ARTS-Laboratory/Drone-Delivered-Vibration-Sensor/system_design/Forth/V0.2.0/Hardware/CAD/Images - In Progress Designs/Permanent Magnet Cap.png

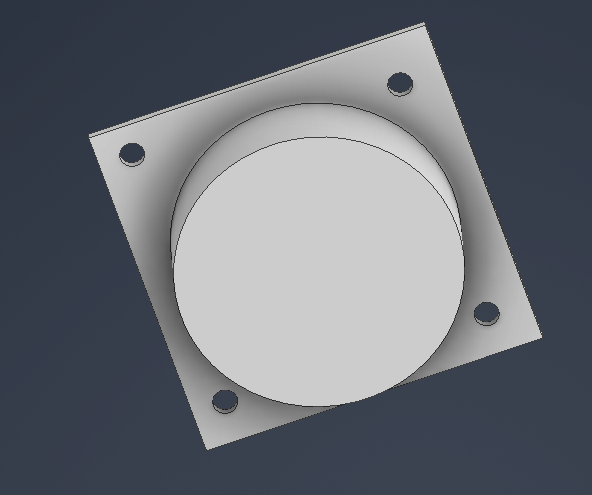
system_design/Forth/V0.2.0/Hardware/CAD/Images - In Progress Designs/Permanent Magnet Cap.png
