ARTS-Laboratory/Drone-Delivered-Vibration-Sensor/system_design/Forth/V0.2.0/Hardware/CAD/Images - In Progress Designs/Standoffs for PCB screws (which of the two options).png

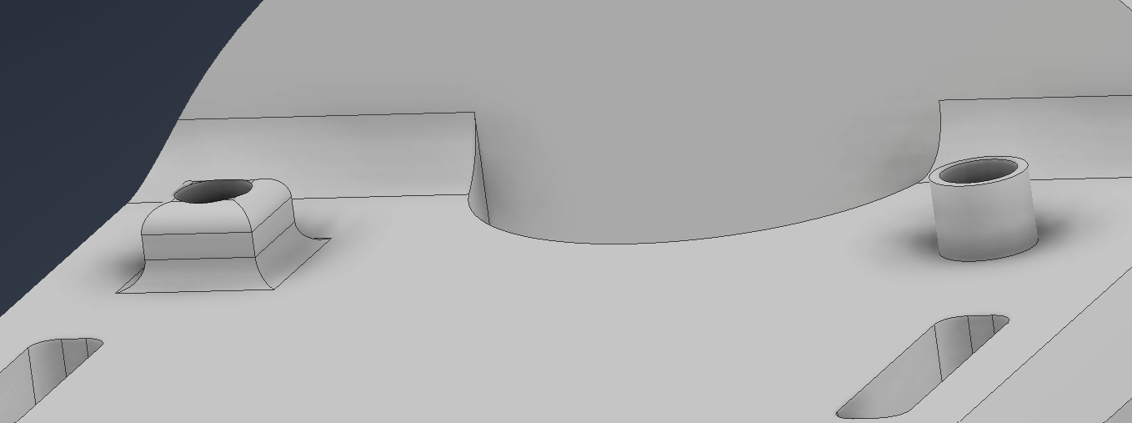
system_design/Forth/V0.2.0/Hardware/CAD/Images - In Progress Designs/Standoffs for PCB screws (which of the two options).png
