ARTS-Laboratory/Drone-Delivered-Vibration-Sensor/system_design/International Gateway/V0.1/Software/Arduino/Shaker Data Collection/001_FFT_Smoothed_Spectrum_Comparison.png

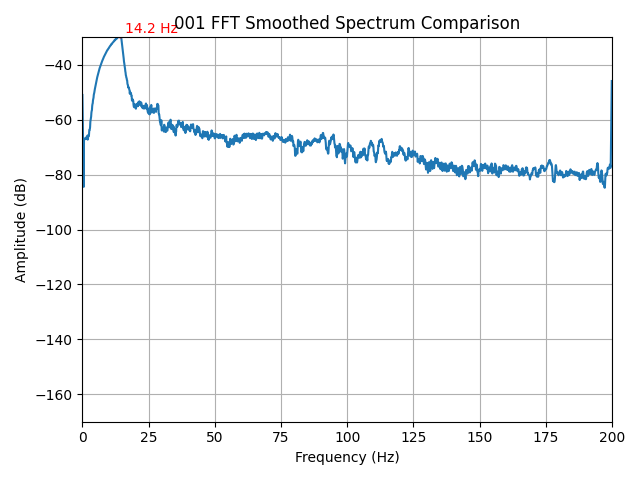
system_design/International Gateway/V0.1/Software/Arduino/Shaker Data Collection/001_FFT_Smoothed_Spectrum_Comparison.png
