ARTS-Laboratory/Drone-Delivered-Vibration-Sensor/system_design/International Gateway/V0.1/Software/Arduino/Shaker Data Collection/005 Training Error vs Epoch.png

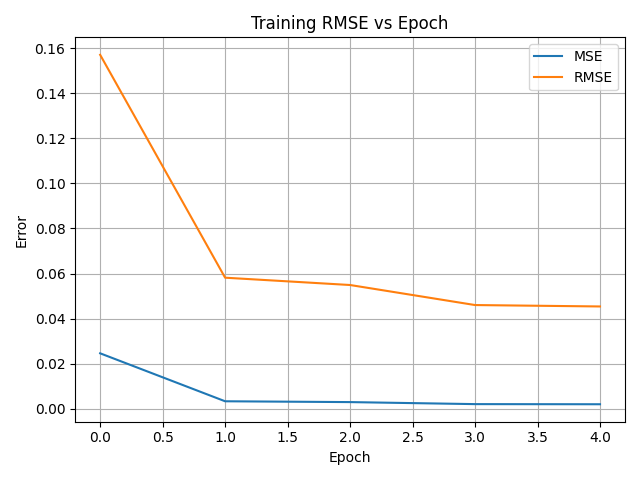
system_design/International Gateway/V0.1/Software/Arduino/Shaker Data Collection/005 Training Error vs Epoch.png
