ARTS-Laboratory/Drone-Delivered-Vibration-Sensor/system_design/International Gateway/V0.1/Software/Arduino/Shaker Data Collection/014_10Epoch_Training_Error_vs_Epoch.png

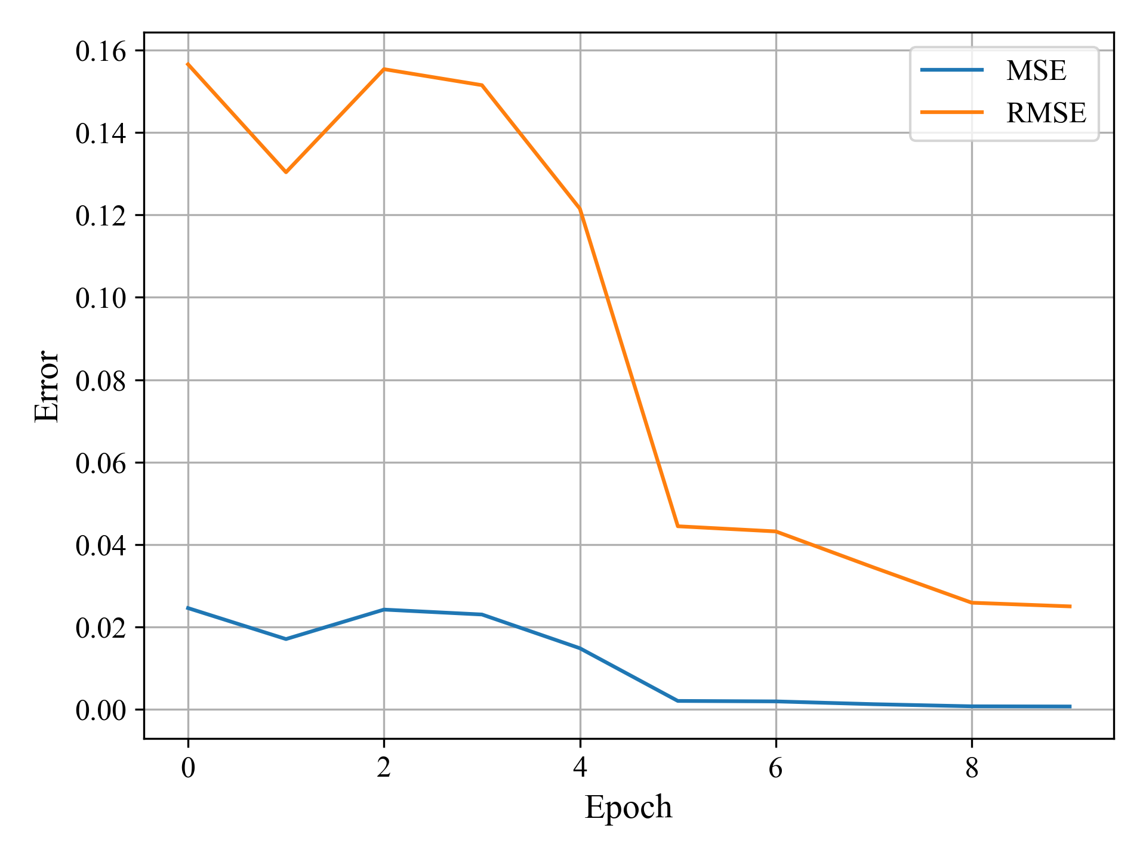
system_design/International Gateway/V0.1/Software/Arduino/Shaker Data Collection/014_10Epoch_Training_Error_vs_Epoch.png
