ARTS-Laboratory/Drone-Delivered-Vibration-Sensor/system_design/International Gateway/V0.1/Software/Arduino/Shaker Data Collection/DATA001_FRF_Magnitude.png

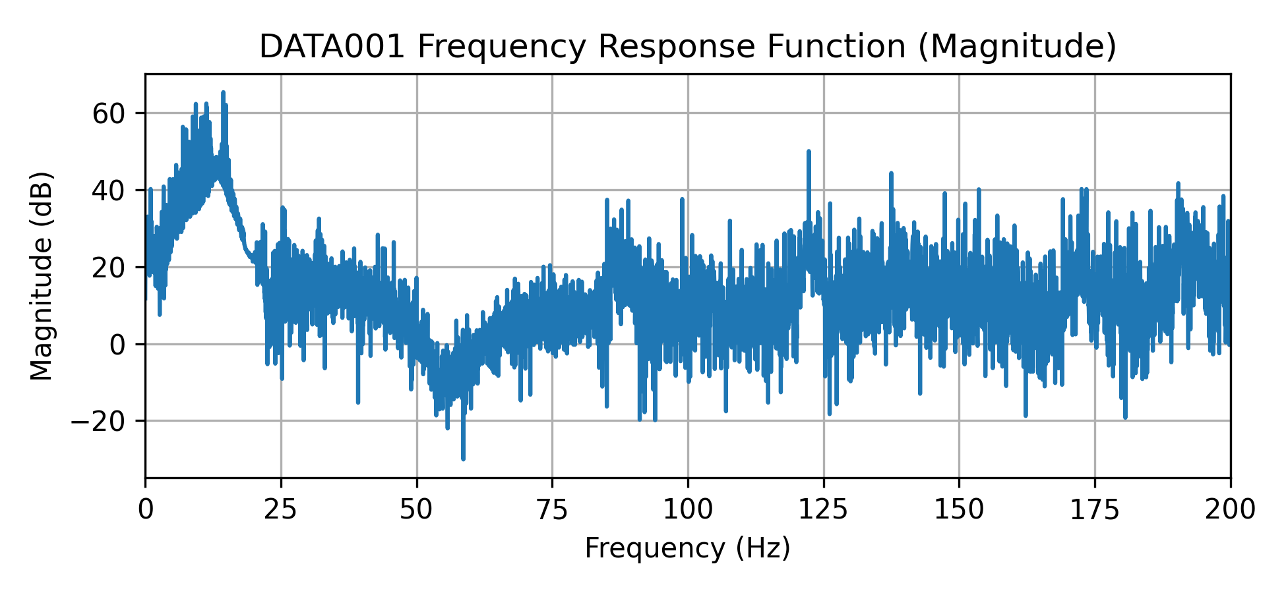
system_design/International Gateway/V0.1/Software/Arduino/Shaker Data Collection/DATA001_FRF_Magnitude.png
