ARTS-Laboratory/Drone-Delivered-Vibration-Sensor/system_design/International Gateway/V0.1/Software/Arduino/Shaker Data Collection/dataset_collection/dataset-collection/improved-dataset-collection/ZoomedInImpulse.png

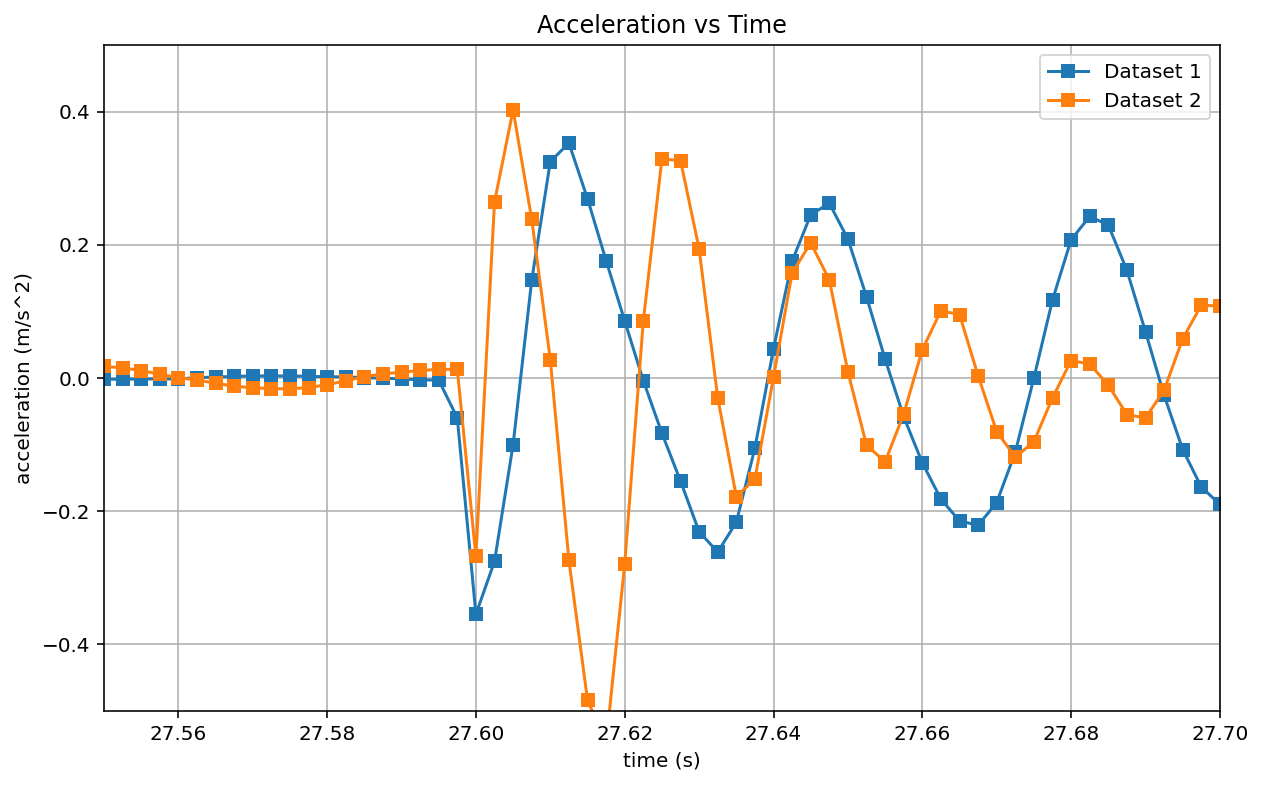
system_design/International Gateway/V0.1/Software/Arduino/Shaker Data Collection/dataset_collection/dataset-collection/improved-dataset-collection/ZoomedInImpulse.png
