ARTS-Laboratory/Drone-Delivered-Vibration-Sensor/system_design/International Gateway/V0.1/Software/Arduino/Shaker Data Collection/Runs/Run_001_Epoch20_Batch16_Window400/014_20Epoch_Zoom_Acceleration_Comparison.png

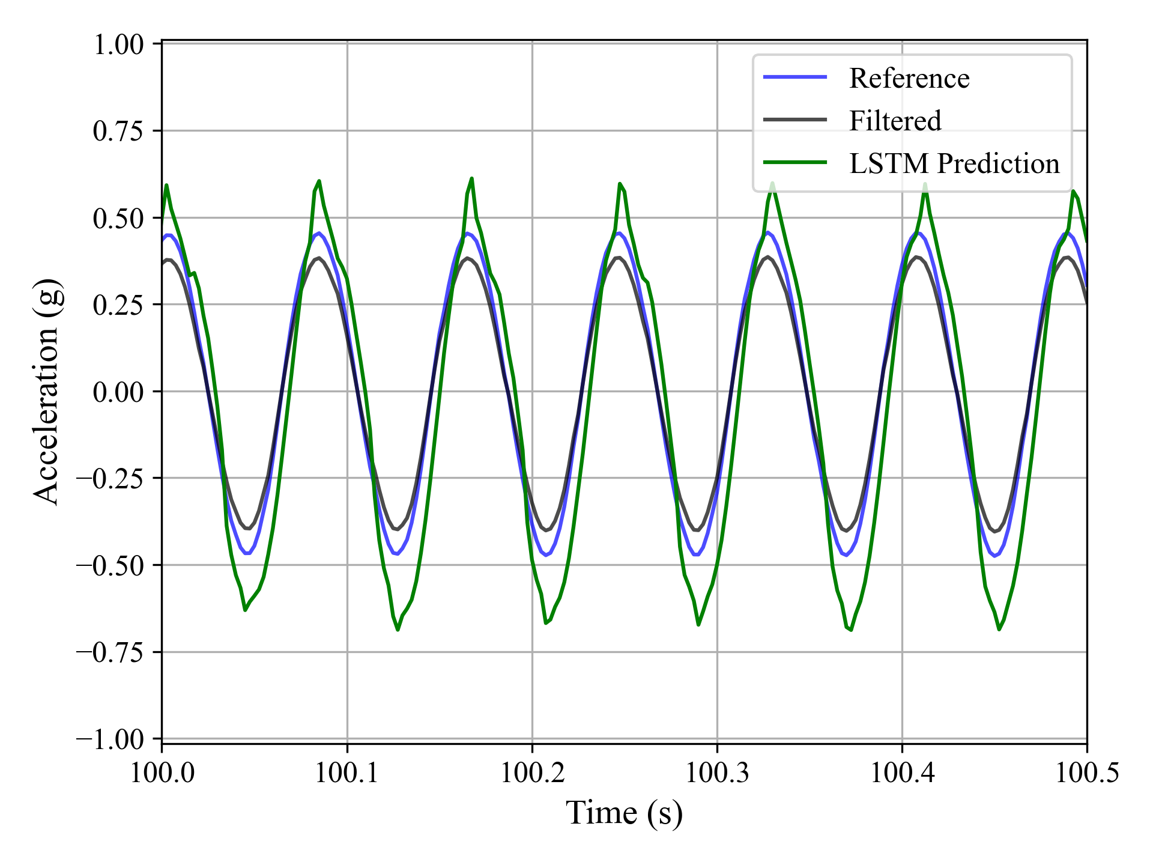
system_design/International Gateway/V0.1/Software/Arduino/Shaker Data Collection/Runs/Run_001_Epoch20_Batch16_Window400/014_20Epoch_Zoom_Acceleration_Comparison.png
