ARTS-Laboratory/Drone-Delivered-Vibration-Sensor/system_design/International Gateway/V0.1/Software/test/reduced.csv

-5.280582979321479797e-02
-6.273836642503738403e-02
-6.120144948363304138e-02
-5.868064984679222107e-02
-5.747686699032783508e-02
-5.670031160116195679e-02
-5.480265989899635315e-02
-5.214745178818702698e-02
-4.811622947454452515e-02
-4.461257904767990112e-02
-3.961358591914176941e-02
-3.492707386612892151e-02
-3.026051446795463562e-02
-2.505939267575740814e-02
-1.904052495956420898e-02
-1.265662536025047302e-02
-5.546108819544315338e-03
7.930994033813476562e-04
7.546235807240009308e-03
1.386597938835620880e-02
2.126452513039112091e-02
2.834310196340084076e-02
3.354794532060623169e-02
3.958639502525329590e-02
4.564755037426948547e-02
5.100083723664283752e-02
5.439259484410285950e-02
5.936903133988380432e-02
6.369995325803756714e-02
6.544636189937591553e-02
6.805902719497680664e-02
6.887361407279968262e-02
6.899196654558181763e-02
6.766168773174285889e-02
6.606276333332061768e-02
6.420896947383880615e-02
6.054136157035827637e-02
5.761456862092018127e-02
5.377897247672080994e-02
4.863581433892250061e-02
4.405733942985534668e-02
3.838369250297546387e-02
3.206370398402214050e-02
2.472146973013877869e-02
1.924117468297481537e-02
1.180394738912582397e-02
3.609195118770003319e-03
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
