ARTS-Laboratory/Drone-Delivered-Vibration-Sensor/system_design/International Gateway/V0.1/Software/test/uncompressed.csv

-2.346628531813621521e-02
-4.012515023350715637e-02
-5.351005122065544128e-02
-6.720842421054840088e-02
-8.011138439178466797e-02
-9.090606123208999634e-02
-9.889101982116699219e-02
-1.043778061866760254e-01
-1.086088269948959351e-01
-1.113042235374450684e-01
-1.120164915919303894e-01
-1.100497022271156311e-01
-1.058954596519470215e-01
-1.001832112669944763e-01
-9.353651106357574463e-02
-8.547334372997283936e-02
-7.548370212316513062e-02
-6.431892514228820801e-02
-5.195856466889381409e-02
-3.988573327660560608e-02
-2.724938839673995972e-02
-1.224021427333354950e-02
3.133099293336272240e-03
1.735226809978485107e-02
3.115513175725936890e-02
4.627240449190139771e-02
6.159320101141929626e-02
7.443114370107650757e-02
8.581387996673583984e-02
9.724640101194381714e-02
1.062897816300392151e-01
1.132814735174179077e-01
1.183985844254493713e-01
1.211772039532661438e-01
1.205646246671676636e-01
1.172411367297172546e-01
1.122154220938682556e-01
1.044882982969284058e-01
9.472470730543136597e-02
8.389565348625183105e-02
7.190800458192825317e-02
5.852592736482620239e-02
4.327798634767532349e-02
2.688993141055107117e-02
9.296176955103874207e-03
-7.254051975905895233e-03
-2.285750024020671844e-02
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
