ARTS-Laboratory/Drone-Delivered-Vibration-Sensor/media/test plot edit2.png

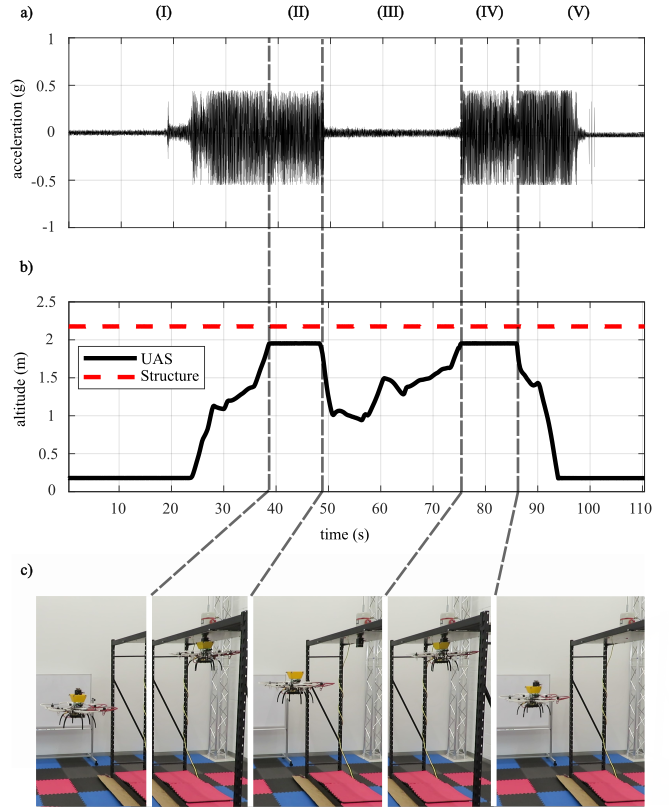
media/test plot edit2.png
