ARTS-Laboratory/Drone-Delivered-Vibration-Sensor/system_design/Brooklyn/V0.5/Hardware/Circuit/main_board/Vibration_Sensor/Vibration_Sensor.kicad_sch

## KiCad design system_design/Brooklyn/V0.5/Hardware/Circuit/main_board/Vibration_Sensor/Vibration_Sensor.kicad_sch (2023-06-23)

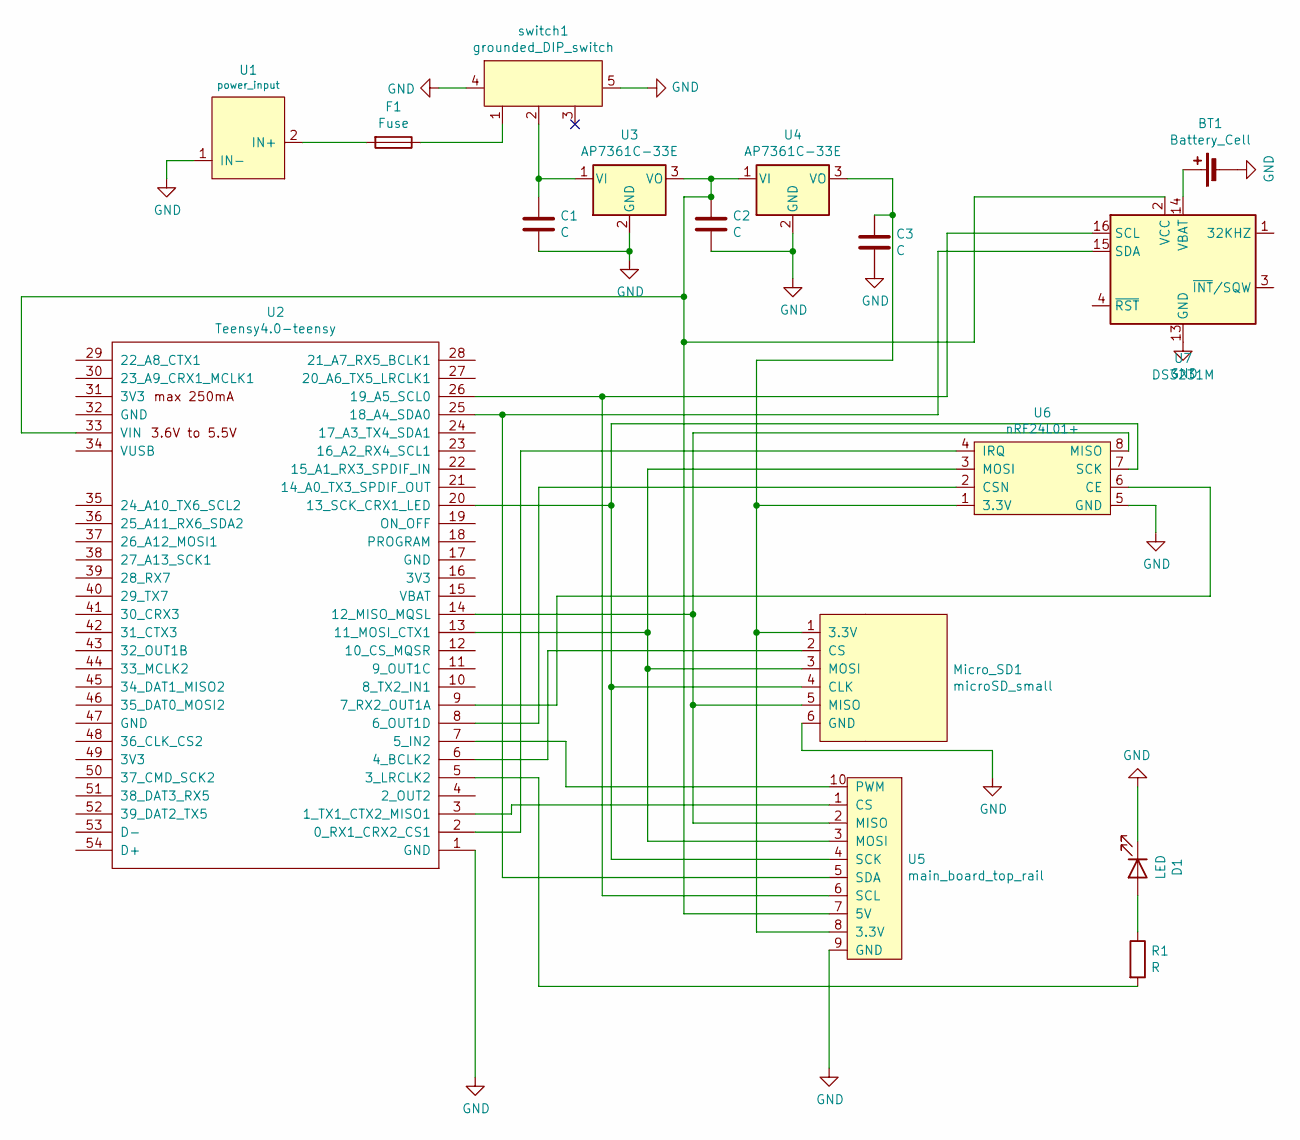
[picture p122: schematic Vibration_Sensor.kicad_sch]

Parts:
BT1: Battery_Cell; battery_holder_10mm
C1, C2, C3: C; C_1206_3216Metric_Pad1.33x1.80mm_HandSolder
D1: LED; LED_D3.0mm
F1: Fuse; C_1206_3216Metric_Pad1.33x1.80mm_HandSolder
Micro_SD1: microSD_small; small_microSD_v2
R1: R; R_1206_3216Metric_Pad1.30x1.75mm_HandSolder
U1: power_input; XT60PW
U2: Teensy4.0-teensy; teensy4.0
U3, U4: AP7361C-33E; SOT-223-3_TabPin2
U5: main_board_top_rail; top_rail
U6: nRF24L01+
U7: DS3231M; SOIC-16W_7.5x10.3mm_P1.27mm
switch1: grounded_DIP_switch; grounded_switch

Connections:
GND: BT1.2 (-), C1.2, C2.2, C3.2, D1.1 (K), Micro_SD1.6 (GND), U1.1 (IN-), U2.1 (GND), U3.2 (GND), U4.2 (GND), U5.9 (GND), U6.5 (GND), U7.5 (GND), U7.6 (GND), U7.7 (GND), U7.8 (GND), U7.9 (GND), U7.10 (GND), U7.11 (GND), U7.12 (GND), U7.13 (GND), switch1.4, switch1.5
unnamed: BT1.1 (+), U7.14 (VBAT)
unnamed: C1.1, U3.1 (VI), switch1.2
unnamed: C2.1, U2.33 (VIN), U3.3 (VO), U4.1 (VI), U5.7 (5V), U7.2 (VCC)
unnamed: C3.1, Micro_SD1.1 (3.3V), U4.3 (VO), U5.8 (3.3V), U6.1 (3.3V)
unnamed: D1.2 (A), R1.1
unnamed: F1.1, switch1.1
unnamed: F1.2, U1.2 (IN+)
unnamed: Micro_SD1.2 (CS), U2.6 (4_BCLK2)
unnamed: Micro_SD1.3 (MOSI), U2.13 (11_MOSI_CTX1), U5.3 (MOSI), U6.3 (MOSI)
unnamed: Micro_SD1.4 (CLK), U2.20 (13_SCK_CRX1_LED), U5.4 (SCK), U6.7 (SCK)
unnamed: Micro_SD1.5 (MISO), U2.14 (12_MISO_MQSL), U5.2 (MISO), U6.8 (MISO)
unnamed: R1.2, U2.5 (3_LRCLK2)
unnamed: U2.2 (0_RX1_CRX2_CS1), U6.4 (IRQ)
unnamed: U2.3 (1_TX1_CTX2_MISO1), U5.1 (CS)
unnamed: U2.7 (5_IN2), U5.10 (PWM)
unnamed: U2.8 (6_OUT1D), U6.2 (CSN)
unnamed: U2.9 (7_RX2_OUT1A), U6.6 (CE)
unnamed: U2.25 (18_A4_SDA0), U5.5 (SDA), U7.15 (SDA)
unnamed: U2.26 (19_A5_SCL0), U5.6 (SCL), U7.16 (SCL)
