ARTS-Laboratory/Drone-Delivered-Vibration-Sensor/system_design/Brooklyn/V0.5/Software/Arduino Code/Long Range Sensor Network/TX/TX.ino

//Include Libraries
#include <SPI.h>
#include <nRF24L01.h>
#include <RF24.h>

//create an RF24 object
RF24 radio(7, 6);  // CE, CSN
//RF24 radio(10, 9);  // CE, CSN Corinne

//address through which two modules communicate.
const byte address[6] = "00001";

int PWM = 2;
int val = 0;
int MAG = 9;

void setup()
{
  Serial.begin(9600);
  pinMode(PWM, INPUT);
  radio.begin();
  
  //set the address
  radio.openWritingPipe(address);
  
  //Set module as transmitter
  radio.stopListening();
}
void loop()
{

  val = 1999; //pulseIn(PWM, HIGH);
  Serial.println(val);

  
  //Send message to receiver
  if (val < 1000 ){
    
  // Package Magnet Control (Charge)
  //const int text3 = 3;
  //radio.write(&text3, sizeof(text3));
  //delay(100);
  }

  else if ((1000<val) && (val<1900)){
  // All Magnets Control (Neutral)   
  //const int text2 = 2;
  //radio.write(&text2, sizeof(text2));
  //delay(100);
  }

  else if (1900<val)  {
  
  //Package Magnet Control(Discharge)    
  const int text1 = 1;
  radio.write(&text1, sizeof(text1));
  delay(3000); 
  }

  else {}

}
