ARTS-Laboratory/Drone-Delivered-Vibration-Sensor/system_design/International Gateway/V0.1/Software/Arduino/Shaker Data Collection/dataset_collection/dataset-collection/dataset-collection.h

// Copyright ARTS Lab, 2024

#ifndef LSTM_COMPENSATION_H
#define LSTM_COMPENSATION_H

#include <SCA3300.h>

using sca3300_library::OperationMode;

void recordData(int16_t* data, uint32_t delayTime);

void writeSDConverted(int16_t* data, OperationMode operationMode, char* fileName);

void printDataConverted(int16_t* data, OperationMode operationMode);

#endif  // LSTM_COMPENSATION_H
