ARTS-Laboratory/Drone-Delivered-Vibration-Sensor/system_design/Forth/V0.2.0/Software/SelfDiagnose/20200813_SCA3300/SCA3300.h

/*
 * Copyright 2020 ARTS Lab @ University of South Carolina
 * Author: Hung-Tien Huang
 */

#ifndef _SCA3300_h
#define _SCA3300_h

#if defined(ARDUINO) && ARDUINO >= 100
#include "arduino.h"
#else
#include "WProgram.h"
#endif

#include <SPI.h>
namespace sca3300_library {
	enum class OperationMode {
		MODE1, MODE2, MODE3, MODE4
	};

	enum class Axis {
		X, Y, Z
	};

	class SCA3300
	{
	private:
		// Table 14 Operations and equivalent SPI frames
		static const byte FRAME_LENGTH = 4;
		static const uint8_t ERROR_VALUE = 255;
		static const uint8_t READ_ACC_X[];
		static const uint8_t READ_ACC_Y[];
		static const uint8_t READ_ACC_Z[];
		static const uint8_t READ_STO[];
		static const uint8_t READ_TEMPERATURE[];
		static const uint8_t READ_STATUS_SUMMARY[];
		static const uint8_t READ_CMD[];
		static const uint8_t CHANGE_TO_MODE1[];
		static const uint8_t CHANGE_TO_MODE2[];
		static const uint8_t CHANGE_TO_MODE3[];
		static const uint8_t CHANGE_TO_MODE4[];
		static const uint8_t SET_POWER_DOWN_MODE[];
		static const uint8_t WAKE_UP_FROM_POWER_DOWN_MODE[];
		static const uint8_t SW_RESET[];
		static const uint8_t READ_WHOAMI[];
		static const uint8_t READ_SERIAL1[];
		static const uint8_t READ_SERIAL2[];
		static const uint8_t READ_CURRENT_BANK[];
		static const uint8_t SWITCH_TO_BANK_ZERO[];
		static const uint8_t SWITCH_TO_BANK_ONE[];

		const uint8_t chipSelect;
		const SPISettings spiSettings;
		OperationMode operationMode;
		bool showLog;

		void send(const uint8_t spiFrame[FRAME_LENGTH], uint8_t ret[FRAME_LENGTH]) const;

		/*
		 * spiFrame[0] & 0b11
		 */
		static const uint8_t getReturnStatus(const uint8_t spiFrame[FRAME_LENGTH]);

		/*
		 * convert data section of the frame back to signed 16-bit integer
		 */
		static const int16_t convertData(const uint8_t spiFrame[FRAME_LENGTH]);

		/*
		 * calculate crc for the given spiFrame
		 * spec p23
		 */
		static const bool checkCRC(const uint8_t spiFrame[FRAME_LENGTH]);

		static const uint8_t crc8(uint8_t bitValue, uint8_t crc);
	public:
		/*
		 * The constructor will only set up instance variable.
		 * User are responsible for calling initChip() to initialize the chip
		 * 
		 * @param chipSelect CS for the SCA3300
		 * @param spiSpeed spi speed for the SCA3300
		 * @param operationMode sca3300_library::SCA3300::OperationMode for the chip
		 * @param showLog print whatever frame received to the serail monitor
		 */
		SCA3300(uint8_t chipSelect, uint32_t spiSpeed, OperationMode operationMode, bool showlog = false);

		/*
		 * Initialize the chip.
		 * If initialization succeed, the method returns ture and vice versa.
		 * 
		 */
		void initChip() const;

		/*
		 * Change operation mode and reinitialize the chip
		 * If change succeed, the method returns true and vice versa.
		 * 
		 * @param operationMode sca3300_library::SCA3300::OperationMode for the chip
		 */
		void chageOperationMode(OperationMode operationMode);

		/*
		* Return current mode that the chip is operating on
		* 
		* @return current operationMode
		*/
		OperationMode getOperationMode() const;

		/*
		 * This method calls READ_STO 2 times and parse the return status
		 * 
		 * @return status = 01, the method returns true and false otherwise.
		 */
		const bool getReturnStatus() const;

		/*
		 * Pass in the interested axis and returns # of g(9.8 m/s^2)
		 * 
		 * if return status is abnormal, reinitialize the chip
		 * 
		 * @param axis sca3300_library::SCA3300::Axis axis to be measured
		 * @return acceleration in # of g(9.8m/s^2)
		 */
		double getAccel(Axis axis) const;

		/*
		 * Pass in the interested axis and returns acceleration
		 * 
		 * if return status is abnormal, reinitialize the chip
		 * 
		 * @param axis sca3300_library::SCA3300::Axis axis to be measured
		 * @return raw acceleration data
		 */
		int16_t getAccelRaw(Axis axis) const;

		/*
		 * This method converts temperature data back to degree celsius.
		 * 
		 * if return status is abnormal, reinitialize the chip
		 *
		 * @return temperatur in celsius
		 */
		double getTemp() const;

		/*
		 * This method gets raw temperature data.
		 * 
		 * if return status is abnormal, reinitialize the chip
		 * 
		 * @return raw temperature data
		 */
		int16_t getTempRaw() const;

		/*
		 * Read who am i
		 * returned value should be 0x51
		 * 
		 * @return who am i received from the SCA3300
		 */
		const uint16_t getWhoAmI() const;

		/*
		 * Convert raw acceleration data to m/s^2
		 * 
		 * @param rawAccel raw data to be converted
		 * @param operationMode mode that the data was collected with
		 * @return converted acceleartion in m/s^2
		 */
		static double convertRawAccelToAccel(int16_t rawAccel, const OperationMode& operationMode);

		/*
		* Convert raw temperature to celsius
		* 
		* @param rawTemp raw data to be converted
		* @return converted temperature in celsius
		*/
		static double convertRawTempToTemp(int16_t rawTemp);

	};

};

#endif
