ARTS-Laboratory/Drone-Delivered-Vibration-Sensor/system_design/International Gateway/V0.1/Software/Arduino/compressed-compensation/linear-algebra.h

// Copyright (c) UofSC ARTS Lab, 2025

#ifndef LINEAR_ALGEBRA_H
#define LINEAR_ALGEBRA_H

float dot(float* v1, float* v2, int length);

// Computes the matrix-vector product and writes the result to an array.
void matvec(float* output, float* matrix, float* vector, int m, int n);

// Performs the DoF matvec. Expects B and C to be flattened and concatenated.
void dofMatvec(float* output, float* b, float* c, float* vector, int m, int n, int r);

float sigmoid(float x);

float hypertan(float x);

#endif  // LINEAR_ALGEBRA_H
