ARTS-Laboratory/Drone-Delivered-Vibration-Sensor/system_design/Brooklyn/V0.5/Software/Arduino Code/Long Range Sensor Network/Dedicated TX perioding ping/RX simple text/RX_simple_text/RX_simple_text.ino

/*
* Arduino Wireless Communication Tutorial
*       Example 1 - Receiver Code
*                
* by Dejan Nedelkovski, www.HowToMechatronics.com
* 
* Library: TMRh20/RF24, https://github.com/tmrh20/RF24/
*/

#include <SPI.h>
#include <nRF24L01.h>
#include <RF24.h>

//RF24 radio(7, 8); // CE, CSN
RF24 radio(7, 6); // CE, CSN

const byte address[6] = "00001";
const int rled = 9;

void setup() {
  pinMode(rled, OUTPUT);
  Serial.begin(9600);
  radio.begin();
  radio.openReadingPipe(0, address);
  radio.setPALevel(RF24_PA_MIN);
  radio.startListening();
}

void loop() {
  digitalWrite(rled, LOW);
//  if (radio.available()) {
//    char text[32] = "";
//    radio.read(&text, sizeof(text));
//    Serial.println(text);
//    digitalWrite(rled, HIGH);
//  }
  while(radio.available()){
    char text[32] = "";
    int msg = 0;
//  radio.read(&text, sizeof(text));
    radio.read(&msg, sizeof(msg));
    //Serial.println(text);
    if(msg == 1){
      digitalWrite(9, HIGH);
      Serial.println(msg);
      delay(500);
    }
  }
}
